fpicarras/TriboSampler/TriboeletricSampler-KiCad/images/TEK00000.PNG

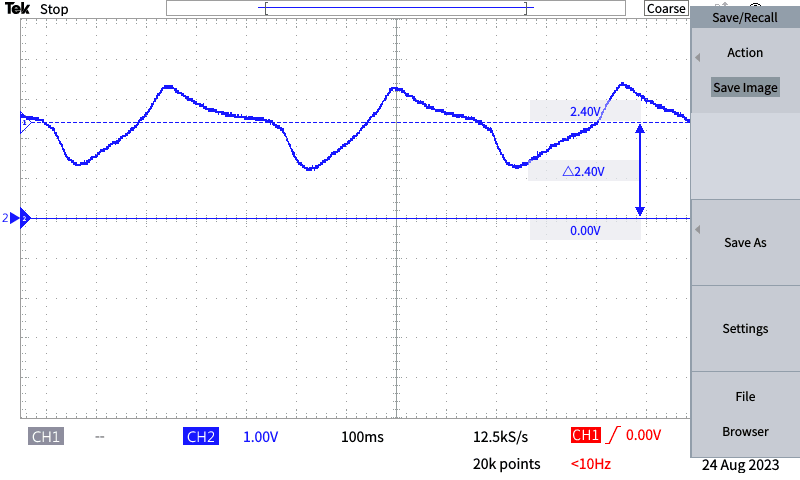
TriboeletricSampler-KiCad/images/TEK00000.PNG
