fpicarras/TriboSampler/TriboeletricSampler-KiCad/images/TEK00004.PNG

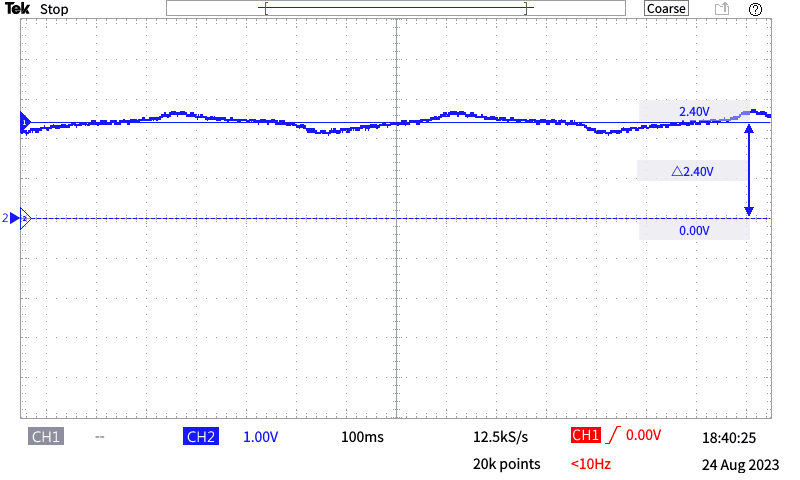
TriboeletricSampler-KiCad/images/TEK00004.PNG
